jmh8231-Dev/ancp/Solid Rocket Motor Test Station - FW/SR Motor Test Station_FW/Drivers/lvgl/docs/src/_static/images/home_5.png

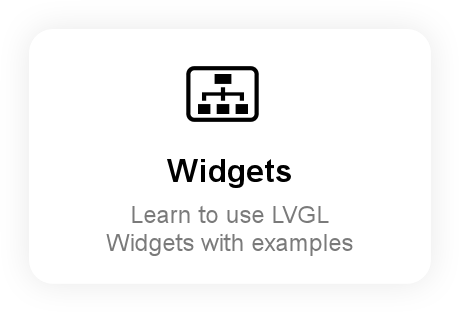
Solid Rocket Motor Test Station - FW/SR Motor Test Station_FW/Drivers/lvgl/docs/src/_static/images/home_5.png
