jmh8231-Dev/ancp/Solid Rocket Motor Test Station - FW/SR Motor Test Station_FW/Drivers/lvgl/tests/ref_imgs/draw/render/al88/demo_render_conical_gradient_opa_255.png

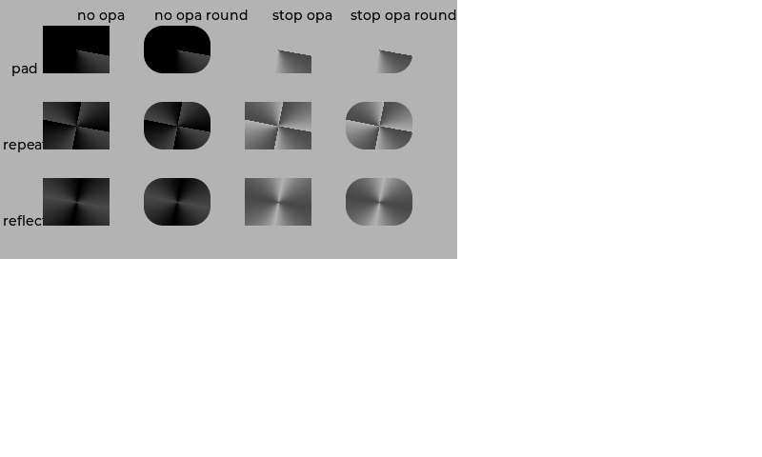
Solid Rocket Motor Test Station - FW/SR Motor Test Station_FW/Drivers/lvgl/tests/ref_imgs/draw/render/al88/demo_render_conical_gradient_opa_255.png
