jmh8231-Dev/ancp/Solid Rocket Motor Test Station - FW/SR Motor Test Station_FW/Drivers/lvgl/tests/ref_imgs_vg_lite/draw/render/argb1555/demo_render_image_normal_2_opa_255.png

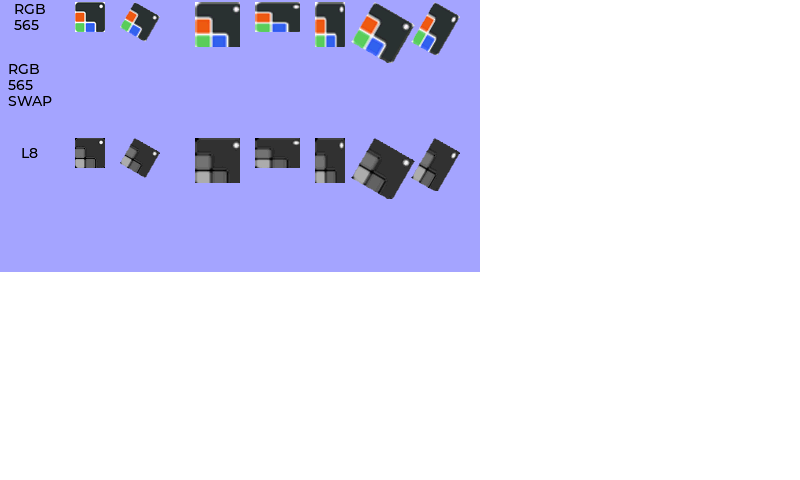
Solid Rocket Motor Test Station - FW/SR Motor Test Station_FW/Drivers/lvgl/tests/ref_imgs_vg_lite/draw/render/argb1555/demo_render_image_normal_2_opa_255.png
