jmh8231-Dev/ancp/Solid Rocket Motor Test Station - FW/SR Motor Test Station_FW/Drivers/lvgl/tests/ref_imgs_vg_lite/draw/render/argb8888/demo_render_blend_mode_opa_128.png

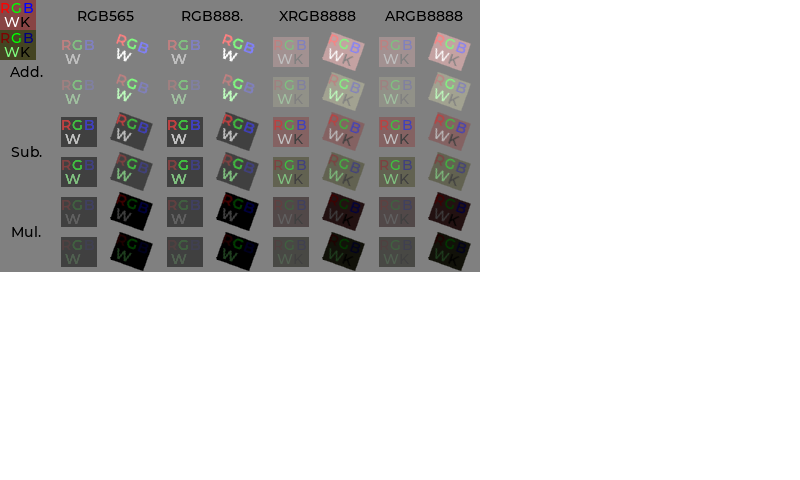
Solid Rocket Motor Test Station - FW/SR Motor Test Station_FW/Drivers/lvgl/tests/ref_imgs_vg_lite/draw/render/argb8888/demo_render_blend_mode_opa_128.png
